ale-ben/Olive-Turtle/Olive-Turtle_manual_control/src/utilities/loggerLib.hpp

/**
 * @file timeLib.cpp
 * @author Alessandro Benetton (aleben98@gmail.com)
 * @author Crespan Lorenzo (lorenzo.crespan@gmail.com)
 * @brief 
 * @version 0.1
 * @date 2023-05-06
 * 
 * @copyright Copyright (c) 2023
 * 
 */

#ifndef LOGGERLIB_HPP
#define LOGGERLIB_HPP
#include <Arduino.h>
void logInfo(const char *module, const char *message);
void logInfo(const char *module, const char *message, const char* value);
void logInfo(const char *module, const char *message, String value);
void logInfo(const char *module, const char *message, int value);
void logInfo(const char *module, const char *message, float value);
void logDebug(const char *module, const char *message);
void logDebug(const char *module, const char *message, const char* value);
void logDebug(const char *module, const char *message, String value);
void logDebug(const char *module, const char *message, int value);
void logDebug(const char *module, const char *message, float value);
void logError(const char *module, const char *message);
void logError(const char *module, const char *message, const char* value);
void logError(const char *module, const char *message, String value);
void logError(const char *module, const char *message, int value);
void logError(const char *module, const char *message, float value);
void logWarning(const char *module, const char *message);
void logWarning(const char *module, const char *message, const char* value);
void logWarning(const char *module, const char *message, String value);
void logWarning(const char *module, const char *message, int value);
void logWarning(const char *module, const char *message, float value);
#endif
